Formula-Student-Switzerland/night-cones/doc/img/CAD_Charging.pdf

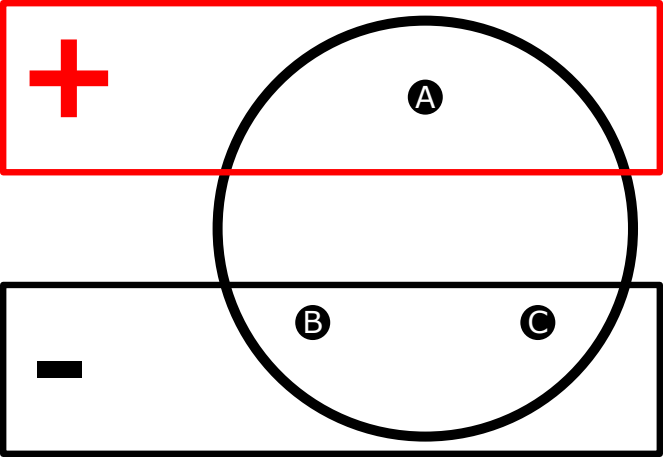
[picture p5: figure]
