Formula-Student-Switzerland/night-cones/doc/img/LogoFSCH-Color.pdf

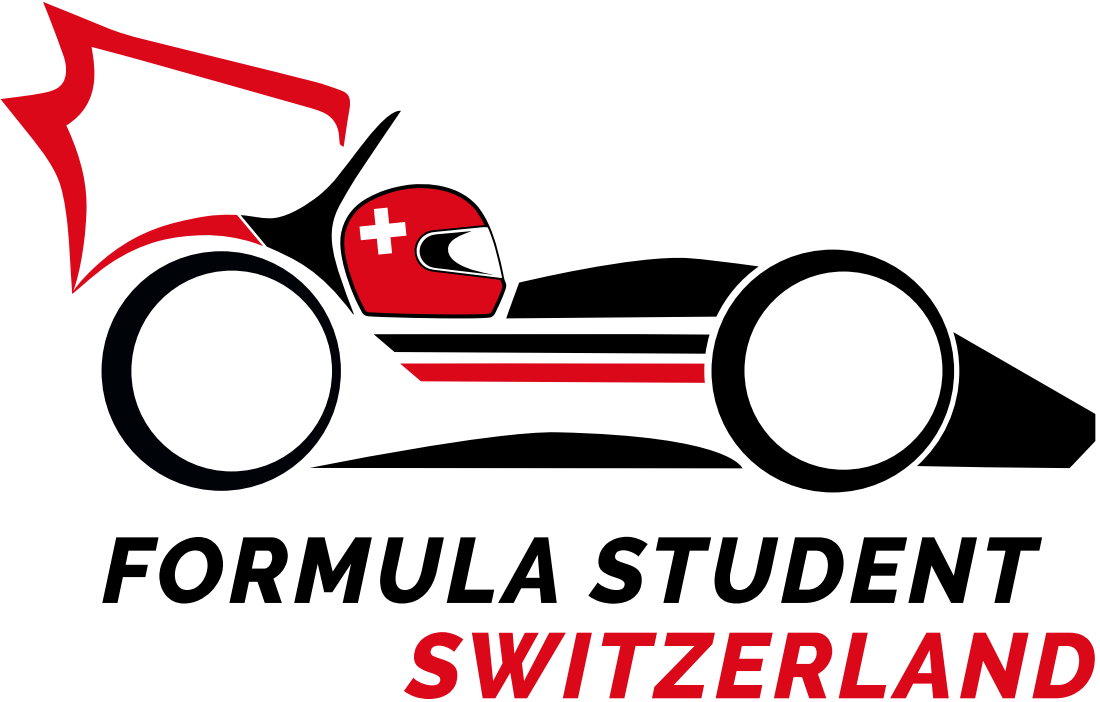
[picture p36: page 1]
