Formula-Student-Switzerland/night-cones/HW/scripts/Kill_Switch.asc

C1: cap; 100n
C2: cap; 1µ
C3: cap; 100n
C4: cap; 1µ
C5: cap; 100n
C6: cap; 1µ
D1: diode; BAS70
D2: diode; BAS70
D3: diode; BAS70
D4: diode; BAS70
I1: current; 5µ
I2: current; 5µ
I3: current; 5µ
R1: res; 270
R2: res; 100k
R3: res; 270
R4: res; 100k
R5: res; 1k
R6: res; 100k
R7: res; 270
V1: voltage; PULSE(0 3.3 100u 1n 1n 50u 100u 50)
V2: voltage; PULSE(0 3.3 100u 1n 1n 50u 100u 50)
V3: voltage; PULSE(0 3.3 100u 1n 1n 50u 100u 50)
Named nets: 0, v_ac, v_ac1, v_ac2, V_ref, v_diode, v_res
.tran 0 20m 0
.LIB BAS70.prm
