Formula-Student-Switzerland/night-cones/SW/client/src/config_store.h

/****************************)***************************************************/
/* 
 * File: config_store.h
 * Author: Andreas Horat
 */
/*******************************************************************************/
/*
 * This file is used to access the EEPROM on the Nightcone Device.
 */
/*******************************************************************************/
#ifndef CONFIG_STORE_H
#define CONFIG_STORE_H
#include <stdint.h>

#define CONFIG_STORE_SW_REV_MAJ 0x1
#define CONFIG_STORE_SW_REV_MIN 0x01

#define CONFIG_STORE_PSVN 0x2 // Version of the persistant storage

#define CONFIG_STORE_HARDWARE_DATA_SIZE 20
#define CONFIG_STORE_USER_SETTINGS_SIZE 44


typedef struct{
    uint8_t hardware_revision;
    uint16_t serial_number;
} hardware_data_t;

typedef struct{
    uint16_t cone_id;
    uint16_t reserved; //For aligning lightmode to 32 bit
    uint8_t fallback_lightmode;
    uint8_t fallback_color;
    uint8_t fallback_phase;
    uint8_t fallback_repetition_time;
    uint16_t status_refresh_period_ms;
    uint16_t turn_off_voltage_mv;
    uint32_t ip_address;
    uint32_t subnet;
    uint32_t gateway; 
} user_settings_t;



typedef struct{
    uint8_t psvn;
    uint8_t header_reserved[7]; // Used to align to page size
    hardware_data_t hardware_data;
    uint8_t hardware_data_reserved[CONFIG_STORE_HARDWARE_DATA_SIZE-sizeof(hardware_data_t)];
    uint32_t hardware_data_crc;
    user_settings_t user_settings;
    uint8_t user_settings_reserved[CONFIG_STORE_USER_SETTINGS_SIZE-sizeof(user_settings_t)];
    uint32_t user_settings_crc;
}  config_store_t;




extern config_store_t config_store;

void config_store_setup(void);

int config_store_read(void);

int config_store_store(void);
int config_store_storeHW(void);

int config_store_get_external(void);

#endif
