Formula-Student-Switzerland/night-cones/SW/client/NC_programmer.py

# Copyright (c) 2024 Andreas Horat
import subprocess
import time
import pyftdi.serialext as serial
import argparse

# NC_programmer.py -s 1 0x2 "../../../esptool/esptool.py" --chip esp8266 --port "ftdi://ftdi:ft-x:0:1/1" --baud 115200 write_flash 0x0 .pio\build\nodemcuv2\firmware.bin


def auto_int(x):
    return int(x, 0)


if __name__ == "__main__":
   
   parser = argparse.ArgumentParser(
                    prog='NC-Programmer',
                    description='Nightcones Programmer for NC3-1AA programmer board.',
                    epilog='Brought to you with <3')
   parser.add_argument('esptool_path', help ="Path to the esptool.py", default="../../../esptool/esptool.py")
   parser.add_argument('-s','--set_EEPROM_config', help="Set EEPROM values ['Serial Number' 'HW Revision']", nargs=2, type=auto_int)  
   parser.add_argument('-p', '--port', help="Serial port device")
   parser.add_argument('-b','--baudrate', help="serial port baudrate (default: 115200)", default=115200)
   args, unknown = parser.parse_known_args()
   print(F"Call: esptool-ftdi.py {args.esptool_path} --port {args.port} --baud {args.baudrate} {' '.join(unknown)}")
   subprocess.call(F"esptool-ftdi.py {args.esptool_path} --port {args.port} {' '.join(unknown)}", shell=True)
   
   if(args.set_EEPROM_config==None):
    exit()
   print("Wait until restarted...\r\n")
   port = serial.serial_for_url(args.port, baudrate=args.baudrate, timeout=2)
   i=0;
   port.flush()
   port.reset_input_buffer()
   time.sleep(4)
   
   c = port.read()
   for i in range(0,2):
    while(c != b">"):
        i = i+1;
        c = port.read()
        #print(c)
        time.sleep(0.01)
        if(i>400):
            print("Error: Device did not properly reboot!")
            #exit()
            break;
   
   
   port.write('readEEPROM\n')
   port.write(F"setSerialNo {args.set_EEPROM_config[0]} {args.set_EEPROM_config[1]}\n")
   port.write('LED 138 2 0 0\n')
   port.write('setLEDFallback\n')
   port.write("saveEEPROM\n")
   port.write('readEEPROM\n')
   port.flush()
   #while port.in_waiting:
   line = port.readline().decode('ascii', 'replace')
   for i in range(0,10):
    while line != "":
            print(F"{line}", end="")
            line = port.readline().decode('ascii', 'replace')
   
   input("Press Enter to turn off cone:")
   
   print("Turn Off Cone.")
   
   port.write("turnOff\n")
   port.flush()
   line = port.readline().decode('ascii', 'replace')
   
   while line != "":
     print(F"{line}", end="")
     line = port.readline().decode('ascii', 'replace')
   
